lab11/nucleum/software/apps/capacitive-touch/capacitive_touch.sch

## EAGLE design software/apps/capacitive-touch/capacitive_touch.sch (2016-06-12)

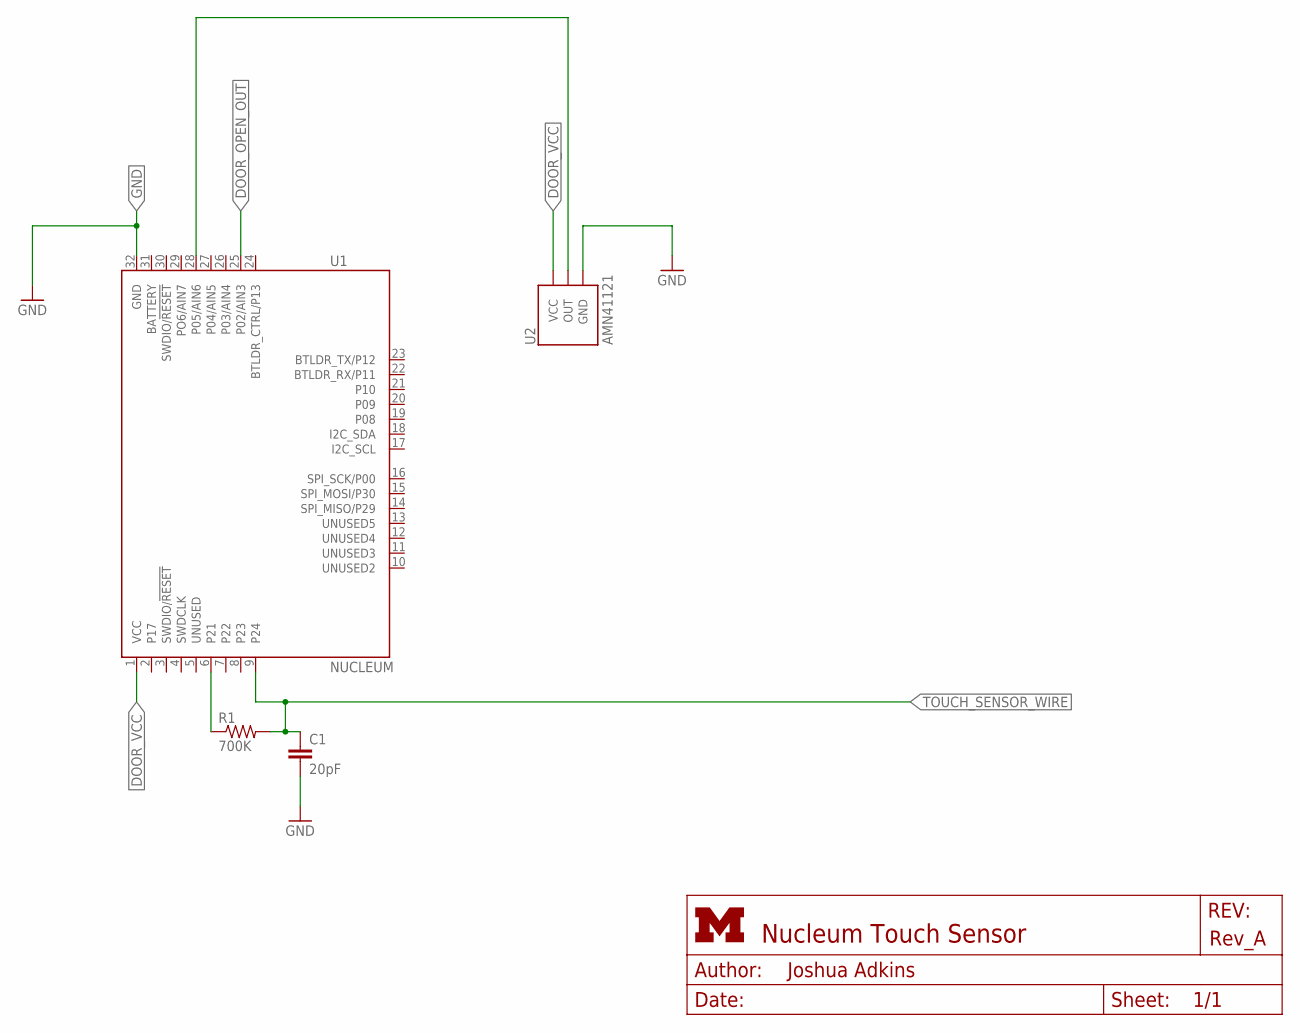
[picture p47: schematic capacitive_touch.sch]

Parts:
C1: 20pF; 1206
R1: 700K; 0603-RES
U1: NUCLEUM
U2: AMN41121; AMN2

Connections:
DOOR_OPEN_OUT: U1.25 (P02/AIN3)
DOOR_VCC: U1.1 (VCC), U2.VCC
GND: C1.2, U1.32 (GND), U2.GND
unnamed: U1.28 (P05/AIN6), U2.OUT
unnamed: R1.1, U1.6 (P21)
TOUCH_SENSOR_WIRE: C1.1, R1.2, U1.9 (P24)
